shanepm98/Ultrasonic-Trilateration/src/apps/ir_accuracy_test/receiver/main/readout_loop.c

/*! \file readout_loop.c
 *
 * \brief Implementation of the IR-triggered pitch-catch receiver. See readout_loop.h.
 *
 * Sensor configuration (measurement queue, icu_gpt algorithm + thresholds, max range, triggered
 * RX-only mode), the data-ready callback, and the IQ_BEGIN/IQ,/IQ_END dump format are identical to
 * pitch_catch_mode_hardware_test/receiver_readout/main/readout_loop.c. Only the trigger path
 * differs: instead of ch_group_trigger() pulsing a hardwired INT1 net shared with the sender, this
 * app fires an IR burst (ir_led.c); this board's own IR demodulator and the sender's each pull
 * their sensor's INT1 low. The ESP32's GPIO2 stays high-impedance the whole time so it never
 * fights the demodulator - which is also why this app must never call ch_trigger()/
 * ch_group_trigger() (SonicLib switches GPIO2 back to a push-pull output when triggering).
 *
 * readout_run() is a console menu ('m' returns to it) over three modes:
 *   1. IR timing tuner (ir_tuner.c) - edits ir_cfg, the waveform used by every later trigger
 *   2. raw I/Q readout - Enter fires one trigger and dumps the I/Q trace
 *   3. distance - Enter fires one trigger and prints one RANGE line
 * On-demand rather than free-running: a ~1.4 KB dump (up to ICU_MAX_NUM_SAMPLES samples x 4 bytes)
 * takes far longer than a measurement over a typical console baud rate - see ../../README.md.
 */

#include "readout_loop.h"

#include <inttypes.h>
#include <stdio.h>
#include <string.h>

#include "freertos/FreeRTOS.h"
#include "freertos/task.h"
#include "freertos/semphr.h"
#include "esp_log.h"
#include <invn/soniclib/soniclib.h>
#include <invn/soniclib/chirp_bsp.h>                /* chbsp_group_set_int1_dir_in() */
#include <invn/soniclib/sensor_fw/icu_gpt/icu_gpt.h> /* icu_gpt_algo_*, InvnAlgoRangeFinderConfig, ch_thresholds_t */

#include "console_io.h"
#include "ir_common.h" /* PC_TX_PULSE_US, PC_ODR, PC_MAX_RANGE_MM, IR_RESPONSE_TIMEOUT_MS */
#include "ir_led.h"
#include "ir_tuner.h"

static const char *TAG = "ir-pitch-catch-rx";

/* ============================ Application configuration ============================ *
 * Same values as pitch_catch_mode_hardware_test/receiver_readout - this RX-only sensor's own noise
 * floor/ringdown is independently tunable from the sender's, and identical starting points make
 * the hardwired- and IR-triggered captures directly comparable on the bench. */

#define RX_GAIN_REDUCE 0u
#define RX_ATTEN       0u

#define RX_RINGDOWN_CANCEL_SAMPLES 20u
#define RX_STATIC_FILTER_SAMPLES   0u
#define RX_NUM_RANGES              1u

static const ch_thresholds_t rx_thresholds = {
    .threshold = {
        {.start_sample = 0, .level = 2500},
        {.start_sample = 30, .level = 1200},
        {.start_sample = 60, .level = 700},
        {.start_sample = 120, .level = 450},
        {.start_sample = 200, .level = 350},
        {.start_sample = 0, .level = 0},
        {.start_sample = 0, .level = 0},
        {.start_sample = 0, .level = 0},
    },
};

static const icu_gpt_algo_config_t rx_gpt_cfg = {
    .ringdown_cancel_samples = RX_RINGDOWN_CANCEL_SAMPLES,
    .static_filter_samples   = RX_STATIC_FILTER_SAMPLES,
    .iq_output_format        = CH_OUTPUT_IQ, /* required for ch_get_iq_data() to return valid data */
    .num_ranges              = RX_NUM_RANGES,
    .filter_update_interval  = 0,
};

/* Raw per-measurement algorithm config the sensor receives; filled by icu_gpt_algo_configure(). */
static InvnAlgoRangeFinderConfig rx_algo_cfg;

/* ============================ Data-ready plumbing ============================ */

typedef struct {
    bool     have_target;
    uint32_t range_q5; /* ch_get_range() units: millimetres * 32 */
    uint16_t amplitude;
    uint16_t num_samples;
    uint8_t  iq_err; /* ch_get_iq_data() return code; 0 = OK */
} readout_summary_t;

/* Only one requested measurement is ever in flight at a time (on-demand triggering), so a single
 * static buffer + summary is enough. A stray ambient-IR trigger can still produce an unrequested
 * measurement; fire_and_wait() drains the semaphore before each burst so that never gets reported
 * as the response to the next request. */
static ch_iq_sample_t     iq_buf[ICU_MAX_NUM_SAMPLES];
static readout_summary_t  summary;
static SemaphoreHandle_t  data_ready_sem;

/* Set by the current mode before triggering: only the raw I/Q mode needs the ~1.4 KB
 * ch_get_iq_data() read, so the distance mode and tuner test shots skip it. */
static volatile bool want_iq;

/* IR trigger waveform used by every trigger; edited by the tuner (mode 1). */
static ir_timing_t ir_cfg;

/* Called by SonicLib after each measurement. Runs in the BSP's bsp_int_task (task level), so
 * blocking SPI reads here - including the I/Q readout - are fine. */
static void readout_data_ready_cb(ch_group_t *grp, uint8_t io_index, ch_interrupt_type_t int_type) {
    if (int_type != CH_INTERRUPT_TYPE_DATA_RDY) {
        return; /* ignore program-loaded / error / other interrupt types */
    }

    ch_dev_t *dev   = ch_get_dev_ptr(grp, io_index);
    uint32_t  range = ch_get_range(dev, CH_RANGE_DIRECT); /* direct pitch-catch: separate objects */

    summary.have_target = (range != CH_NO_TARGET);
    summary.range_q5    = range;
    summary.amplitude   = summary.have_target ? ch_get_amplitude(dev) : 0;
    summary.num_samples = ch_get_num_samples(dev);
    if (summary.num_samples > ICU_MAX_NUM_SAMPLES) {
        summary.num_samples = ICU_MAX_NUM_SAMPLES; /* defensive; shouldn't happen at PC_MAX_RANGE_MM */
    }

    summary.iq_err = want_iq ? ch_get_iq_data(dev, iq_buf, 0, summary.num_samples, CH_IO_MODE_BLOCK) : 0;

    xSemaphoreGive(data_ready_sem);
}

/* ============================ Configuration ============================ *
 * Identical to pitch_catch_mode_hardware_test's receiver - see that app's README for the
 * segment-timing rationale. */

static int readout_configure(ch_dev_t *dev) {
    uint8_t err = 0;

    ch_meas_config_t meas_cfg = {
        .odr         = PC_ODR,
        .meas_period = 0, /* not used in triggered mode */
        .mode        = CH_MEAS_MODE_ACTIVE,
    };
    err |= ch_meas_init(dev, CH_DEFAULT_MEAS_NUM, &meas_cfg, NULL);

    /* GPT rangefinding algorithm + thresholds */
    err |= icu_gpt_algo_init(dev, &rx_algo_cfg);
    err |= icu_gpt_algo_configure(dev, CH_DEFAULT_MEAS_NUM, &rx_gpt_cfg, &rx_thresholds);

    /* Measurement queue: count (matching the sender's TX burst duration) -> receive, no
     * transmit segment - see AN-000175 ("Count Segments"). */
    uint16_t tx_match_cycles = (uint16_t)ch_usec_to_cycles(dev, PC_TX_PULSE_US);
    err |= ch_meas_add_segment_count(dev, CH_DEFAULT_MEAS_NUM, tx_match_cycles, 0);
    err |= ch_meas_add_segment_rx(dev, CH_DEFAULT_MEAS_NUM, ICU_MAX_NUM_SAMPLES, RX_GAIN_REDUCE, RX_ATTEN,
                                  1 /* done interrupt on the last RX segment */);
    err |= ch_meas_write_config(dev);

    /* Push the algorithm configuration to the sensor */
    err |= ch_set_algo_config(dev, &rx_algo_cfg);
    err |= ch_init_algo(dev);

    /* High-level settings; ch_set_mode() must be last - it starts sensing (arms the sensor to
     * react to the next INT1 trigger edge from this board's IR demodulator). */
    err |= ch_set_max_range(dev, PC_MAX_RANGE_MM);
    err |= ch_set_mode(dev, CH_MODE_TRIGGERED_RX_ONLY);

    return err ? -1 : 0;
}

/* ============================ Raw I/Q dump ============================ */

static void print_iq_dump(uint32_t meas_num) {
    if (summary.iq_err != 0) {
        ESP_LOGW(TAG, "#%" PRIu32 "  ch_get_iq_data() failed, err=%u - no dump", meas_num, summary.iq_err);
        return;
    }

    /* Trailing timing fields record the IR waveform each capture was taken with; the host parser
     * (host/extract_measurements.py) ignores them. */
    if (summary.have_target) {
        printf("IQ_BEGIN meas=%" PRIu32 " num_samples=%u target=1 range_mm=%.1f amp=%u", meas_num,
               summary.num_samples, summary.range_q5 / 32.0f, summary.amplitude);
    } else {
        printf("IQ_BEGIN meas=%" PRIu32 " num_samples=%u target=0 range_mm=NA amp=0", meas_num,
               summary.num_samples);
    }
    printf(" pre_on_us=%" PRIu32 " pre_off_us=%" PRIu32 " trig_us=%" PRIu32 "\n",
           ir_cfg.pre_enabled ? ir_cfg.pre_on_us : 0, ir_cfg.pre_enabled ? ir_cfg.pre_off_us : 0,
           ir_cfg.trigger_us);
    for (uint16_t i = 0; i < summary.num_samples; i++) {
        printf("IQ,%u,%d,%d\n", i, iq_buf[i].i, iq_buf[i].q);
    }
    printf("IQ_END\n");
}

/* ============================ Distance line ============================ */

static void print_range(uint32_t meas_num) {
    if (summary.have_target) {
        printf("RANGE meas=%" PRIu32 " target=1 range_mm=%.1f amp=%u\n", meas_num, summary.range_q5 / 32.0f,
               summary.amplitude);
    } else {
        printf("RANGE meas=%" PRIu32 " target=0 range_mm=NA amp=0\n", meas_num);
    }
}

/* ============================ Triggering ============================ */

/* Fire one IR trigger with timing t and wait for this board's data-ready. Returns true if the
 * sensor responded within IR_RESPONSE_TIMEOUT_MS. Requires ir_led_init() and the data-ready
 * callback to be set up (readout_run()). */
static bool fire_and_wait(const ir_timing_t *t) {
    /* Discard any measurement a stray ambient-IR trigger produced since the last request. */
    if (xSemaphoreTake(data_ready_sem, 0) == pdTRUE) {
        ESP_LOGW(TAG, "discarding an unrequested measurement (stray IR trigger?)");
    }

    /* Both demodulators - this board's and the sender's - pull their sensor's INT1 low. */
    esp_err_t err = ir_led_fire(t);
    if (err != ESP_OK) {
        ESP_LOGE(TAG, "ir_led_fire() failed: %s", esp_err_to_name(err));
        return false;
    }
    return xSemaphoreTake(data_ready_sem, pdMS_TO_TICKS(IR_RESPONSE_TIMEOUT_MS)) == pdTRUE;
}

/* Tuner test shot: no I/Q readout needed, only whether the sensor responded. */
static bool tuner_fire(const ir_timing_t *t) {
    want_iq = false;
    return fire_and_wait(t);
}

/* ============================ Modes 2 and 3 ============================ */

/* Enter fires one measurement and prints it (I/Q dump or RANGE line); 'm' returns to the menu. */
static void run_measure_mode(bool iq_mode) {
    static uint32_t n = 0; /* measurement counter, shared across modes and menu visits */

    printf("\n=== %s ===\nIR: ", iq_mode ? "Raw I/Q readout" : "Distance");
    ir_timing_print(&ir_cfg);
    printf("\n[Enter] fire trigger   [m] menu\n");

    for (;;) {
        int c = console_getc();
        if (c == 'm' || c == 'M') {
            return;
        }
        if (!console_is_enter(c)) {
            continue;
        }

        want_iq = iq_mode;
        n++;
        if (!fire_and_wait(&ir_cfg)) {
            ESP_LOGW(TAG, "#%" PRIu32 "  no INT2 within %u ms - check IR LED / demodulator / INT1 wiring",
                     n, (unsigned)IR_RESPONSE_TIMEOUT_MS);
            continue;
        }

        if (iq_mode) {
            print_iq_dump(n);
        } else {
            print_range(n);
        }
    }
}

/* ============================ Public entry point ============================ */

void readout_run(ch_group_t *grp, ch_dev_t *dev) {
    data_ready_sem = xSemaphoreCreateBinary();
    if (data_ready_sem == NULL) {
        ESP_LOGE(TAG, "semaphore alloc failed - halting");
        for (;;) {
            vTaskDelay(portMAX_DELAY);
        }
    }

    /* Release GPIO2 to high-impedance (input, no pulls - chbsp_esp32_init() disables them) so the
     * IR demodulator alone drives INT1. Depends on chbsp_esp32_init() having configured the pin. */
    chbsp_group_set_int1_dir_in(grp);

    ch_io_int_callback_set(grp, readout_data_ready_cb);

    ESP_LOGI(TAG, "configuring: triggered RX-only, max range %u mm", PC_MAX_RANGE_MM);
    if (readout_configure(dev) != 0) {
        ESP_LOGE(TAG, "sensor configuration failed - halting");
        for (;;) {
            vTaskDelay(portMAX_DELAY);
        }
    }
    ESP_LOGI(TAG, "configured: op freq %" PRIu32 " Hz, %u active samples, max range %u mm",
             ch_get_frequency(dev), ch_get_num_samples(dev), ch_get_max_range(dev));

    esp_err_t led_err = ir_led_init();
    if (led_err != ESP_OK) {
        ESP_LOGE(TAG, "ir_led_init() failed: %s - halting", esp_err_to_name(led_err));
        for (;;) {
            vTaskDelay(portMAX_DELAY);
        }
    }

    console_init();
    ir_cfg = ir_timing_default();

    for (;;) {
        printf("\n=== IR pitch-catch receiver ===\nIR: ");
        ir_timing_print(&ir_cfg);
        printf("\n  1) IR timing tuner\n  2) Raw I/Q readout\n  3) Distance\nselect mode: ");
        fflush(stdout);

        int c;
        do {
            c = console_getc();
        } while (c < '1' || c > '3');
        printf("%c\n", c);

        switch (c) {
        case '1':
            ir_tuner_run(&ir_cfg, tuner_fire);
            break;
        case '2':
            run_measure_mode(true);
            break;
        case '3':
            run_measure_mode(false);
            break;
        }
    }
}
